Ferivas/DISPLAYRG/bootloader/include/optiboot_config.h

/*
 * Display SAC-A Optiboot Configuration
 * ATMEGA328P @ 7.3728 MHz, LED on PC2 (active high)
 */
#ifndef OPTIBOOT_CONFIG_H
#define OPTIBOOT_CONFIG_H

#define LED C2
#define LED_START_FLASHES 3
#define BAUD_RATE 38400
#define UART 0

#endif /* OPTIBOOT_CONFIG_H */
